mikrotron-zg/ecotron/hardware/IteaduinoSensorShield.dxf

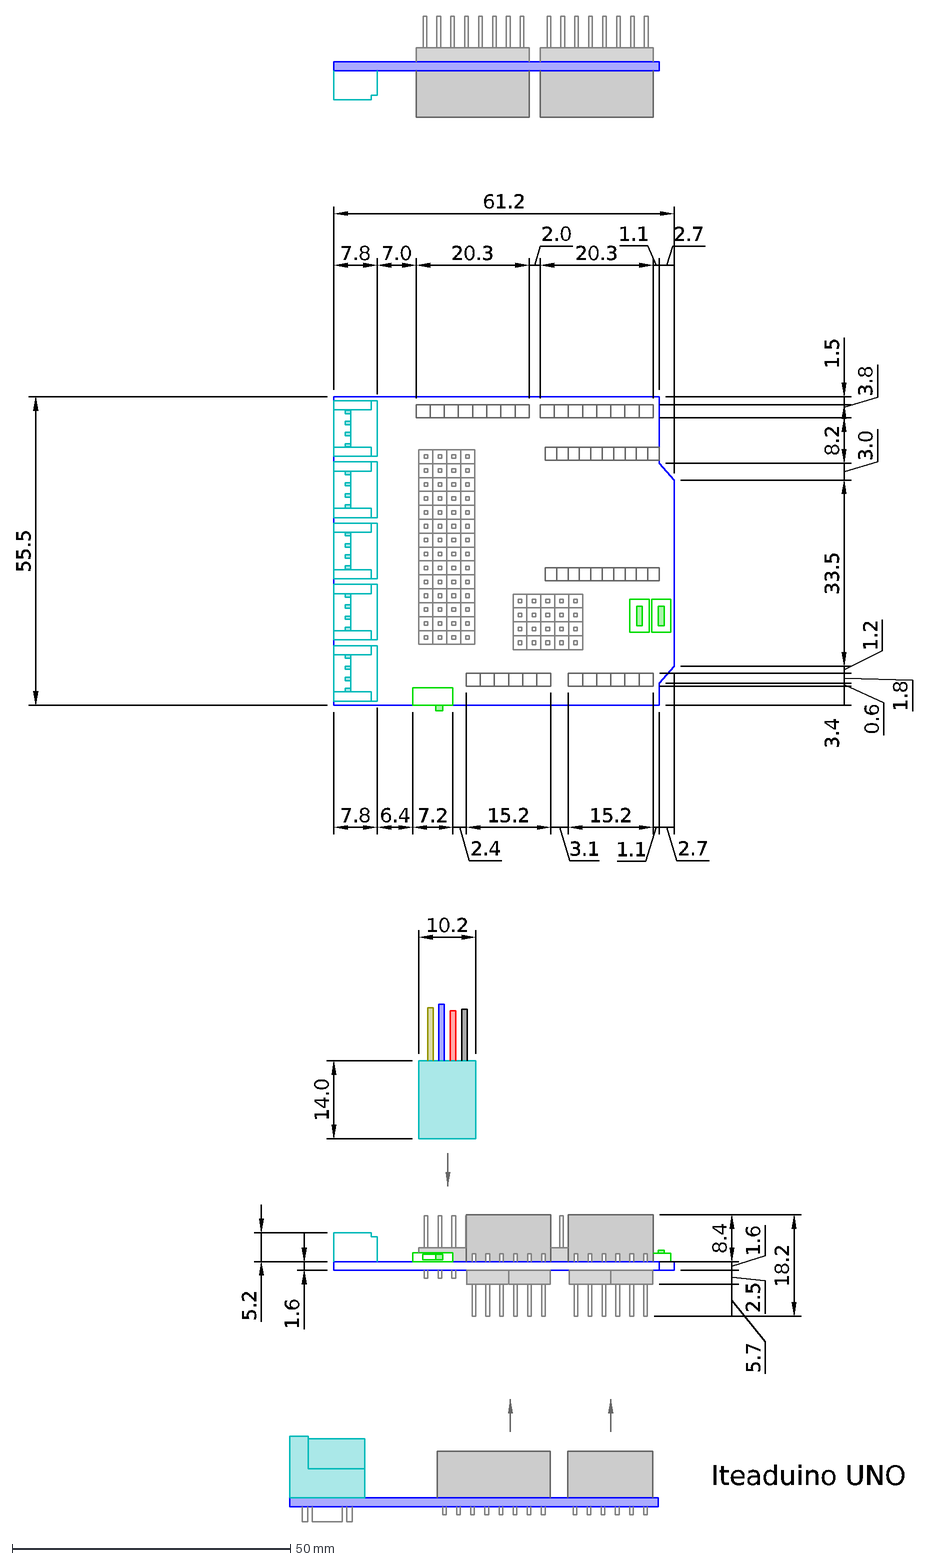
[picture p19: CAD file, 2016-08-19]
hardware/IteaduinoSensorShield.dxf
55.5
1.5
3.8
8.2
3.0
33.5
1.2
1.8
0.6
3.4
61.2
7.8
7.0
20.3
2.0
1.1
2.7
6.4
7.2
2.4
15.2
3.1
18.2
5.2
1.6
8.4
2.5
5.7
14.0
10.2
Iteaduino UNO
